TheSuxarick/ARIA/helpful_utils_for_development/bulb_control.py

# from yeelight import discover_bulbs

# # This scans your network and finds all Yeelight bulbs
# bulbs = discover_bulbs()

# for bulb in bulbs:
#     print(f"Found bulb: {bulb}")
#     print(f"  IP: {bulb['ip']}")
#     print(f"  Port: {bulb['port']}")
#     print(f"  Model: {bulb['capabilities'].get('model', 'unknown')}")



# 172.16.255.52
from yeelight import Bulb
from yeelight.flows import random_loop, disco, lsd

# Replace with your bulb's IP address
bulb = Bulb("10.72.61.149")
# bulb = Bulb("10.72.61.149")



# # Turn on
# bulb.turn_on()

# # Turn off
# bulb.turn_off()

# Toggle
bulb.toggle()

# # Set brightness (1-100)
# bulb.set_brightness(100)
# bulb.set_brightness(100)


# # Set color temperature (1700-6500K)
# bulb.set_color_temp(3000)

# bulb.set_color_temp(4000)  # neutral white

# # Set RGB color (red example)
# bulb.set_rgb(255, 0, 0)

# # Get bulb status
# properties = bulb.get_properties()
# print(properties)


flow = random_loop(duration=750, brightness=100, count=9)
bulb.start_flow(flow)
